kenventions/nmtower/pics/nmTower_pic02_ping.jpg

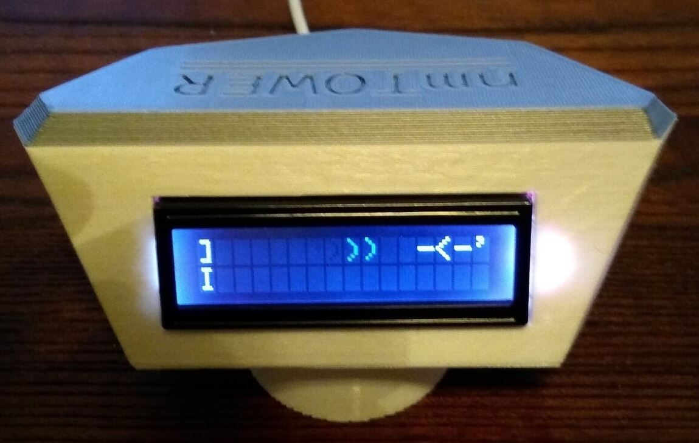
pics/nmTower_pic02_ping.jpg
