kenventions/nmtower/pics/nmTower_pic08_insideview.jpg

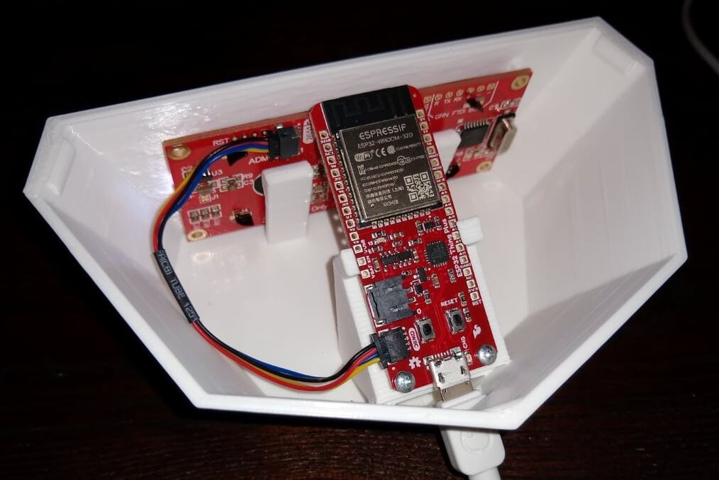
pics/nmTower_pic08_insideview.jpg
