kenventions/nmtower/pics/nmTower_pic09_housingtrim.jpg

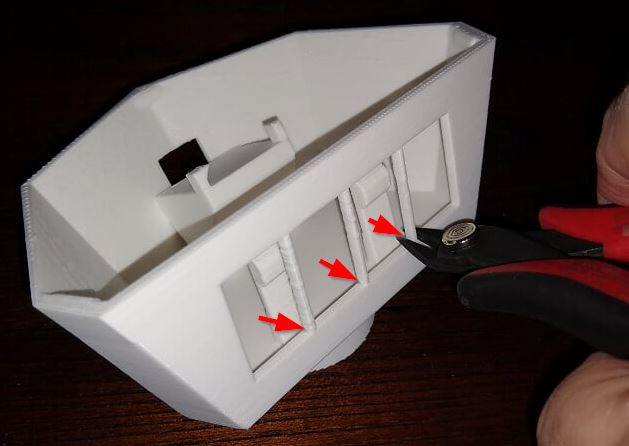
pics/nmTower_pic09_housingtrim.jpg
